PY1CX/Ultra-Mega-PowerSupply/Simulation/0-30-to-0-4v5-VoltageSense.asc

R3: res; 100k
R5: res; 20k
R7: res; 2k
R10: res; 6k
R11: res; 12k
U3: LT6201
V1: voltage; -0.56v
V2: voltage; PULSE(0 30 0 1 1 0 0 5)
V3: voltage; 1.12
V6: voltage; 5v
Named nets: 0
.tran 5
